Anthilla/AnthC/AnthC/Doc/Certifications/certification-mark-IT000014-wide.png

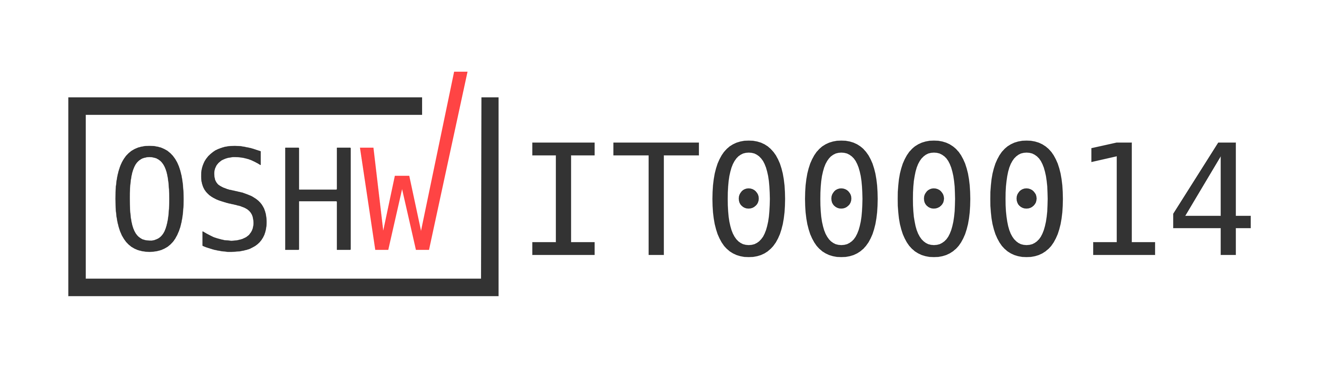
AnthC/Doc/Certifications/certification-mark-IT000014-wide.png
