Anthilla/AnthC/Marketing/Photos/M2-R1/_DSC0009.JPG

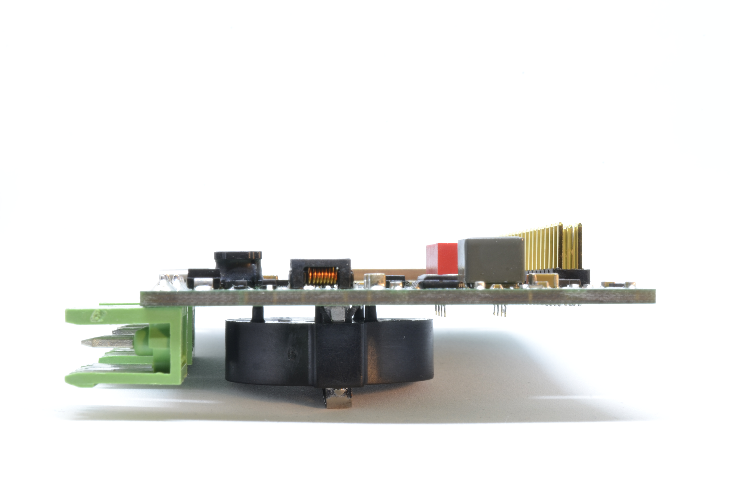
Marketing/Photos/M2-R1/_DSC0009.JPG
