Anthilla/AnthC/Marketing/Photos/M2-R1/_DSC0019.JPG

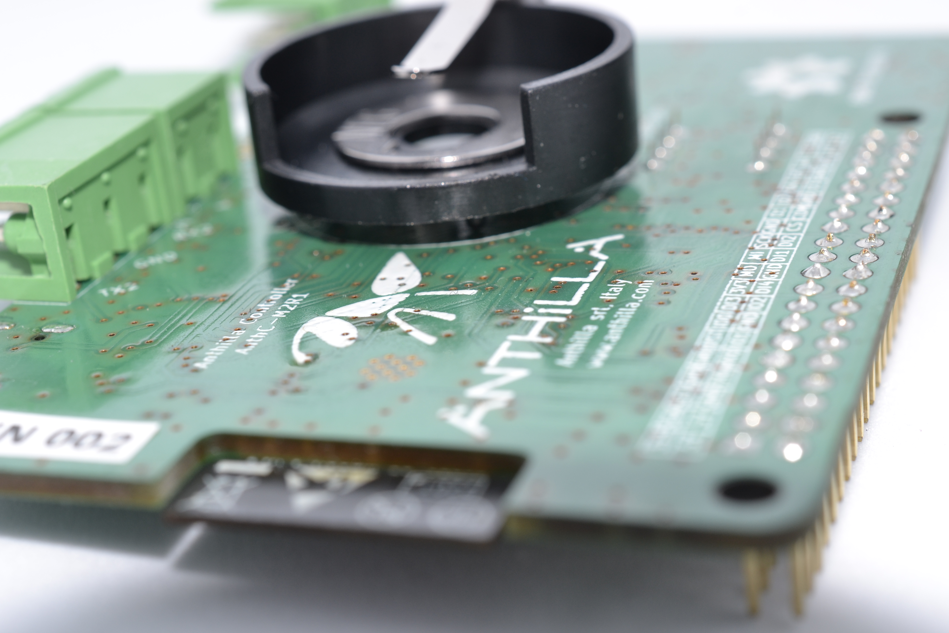
Marketing/Photos/M2-R1/_DSC0019.JPG
