Anthilla/AnthC/Marketing/Photos/M2-R1/_DSC0020.JPG

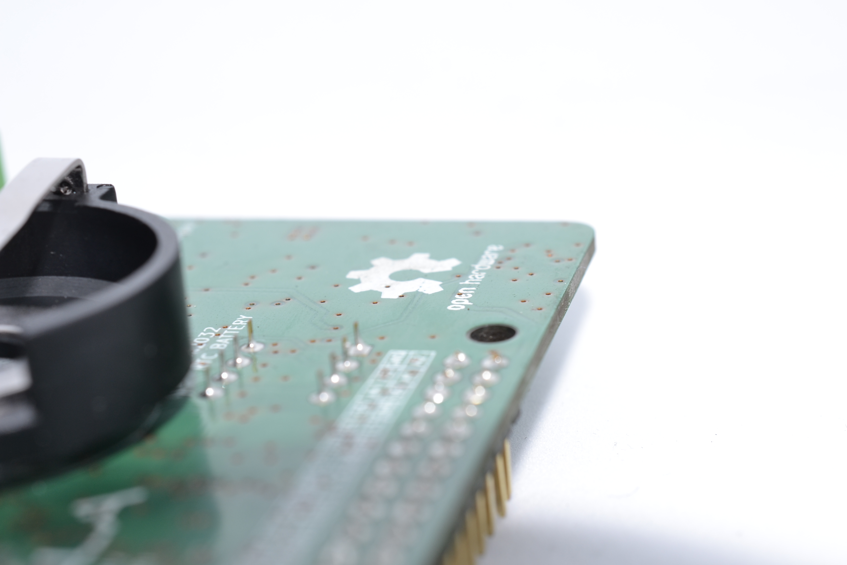
Marketing/Photos/M2-R1/_DSC0020.JPG
