Anthilla/AnthC/Marketing/Photos/M2-R1/_DSC0022.JPG

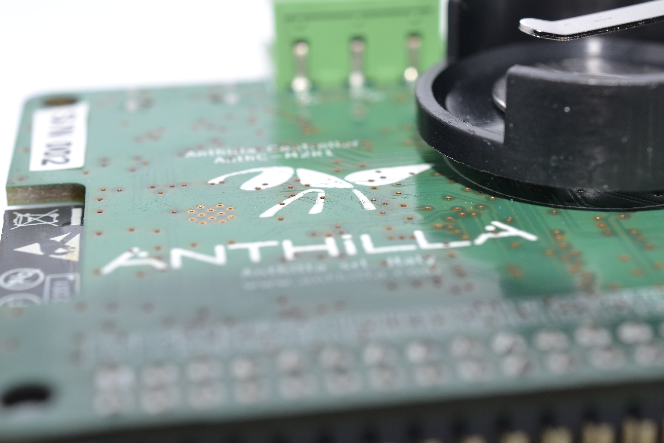
Marketing/Photos/M2-R1/_DSC0022.JPG
